DieMetRik/mercury_esphome/wemos/Schemes/Level.jpeg

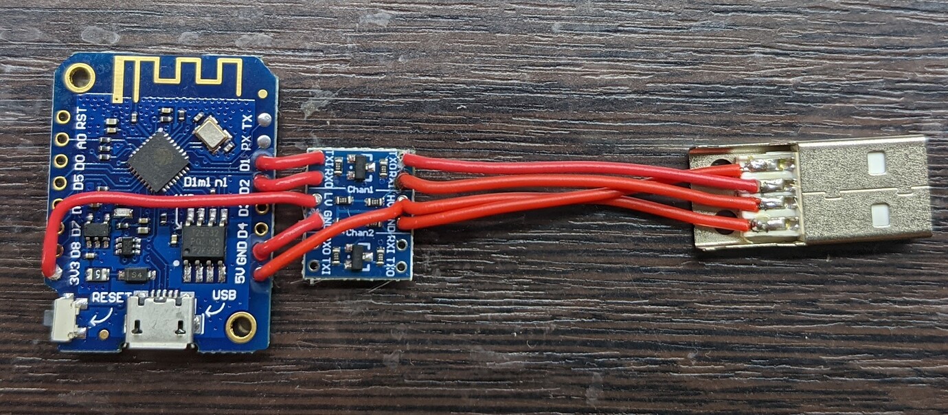
wemos/Schemes/Level.jpeg
